scheetznicholas/cat6-cable-raceway/previews/cableraceway_plate_1.png

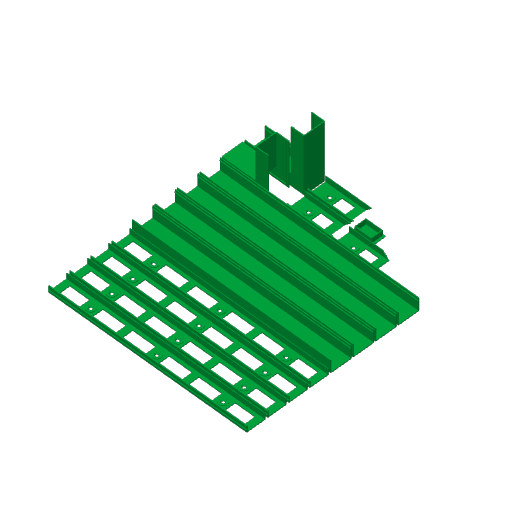
previews/cableraceway_plate_1.png
