scheetznicholas/cat6-cable-raceway/previews/cableraceway_plate_2.png

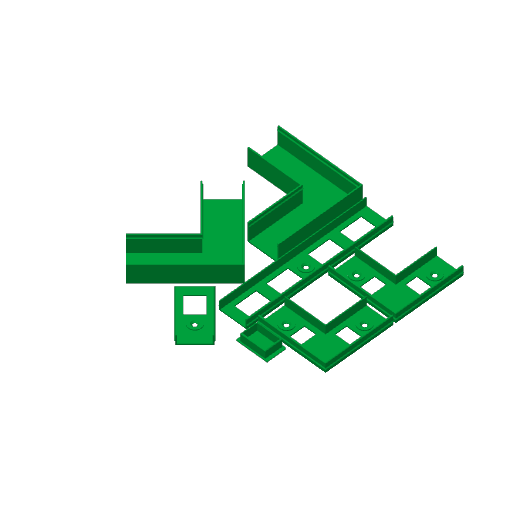
previews/cableraceway_plate_2.png
