scheetznicholas/cat6-cable-raceway/previews/corner_inside_base_stub_iso.png

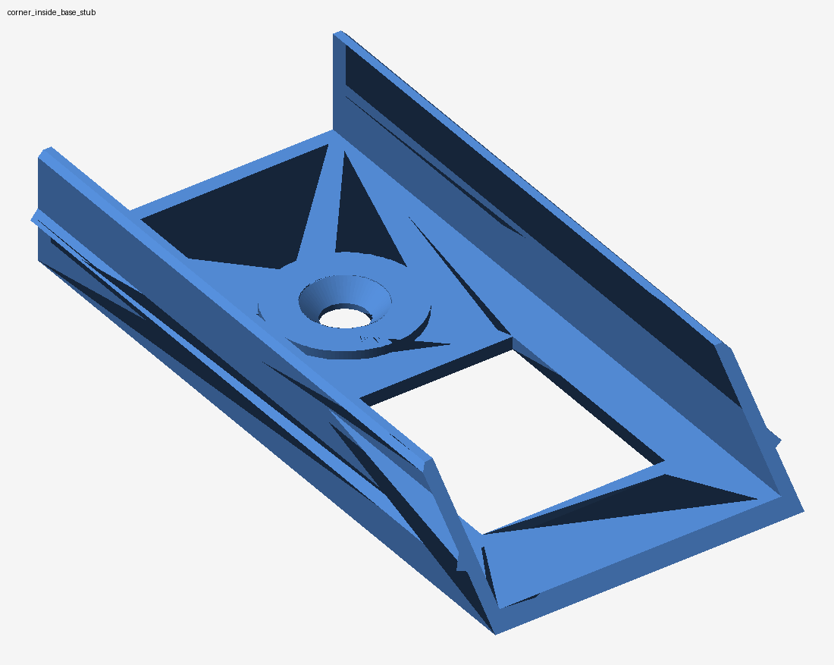
previews/corner_inside_base_stub_iso.png
