scheetznicholas/cat6-cable-raceway/previews/corner_inside_base_stub_under.png

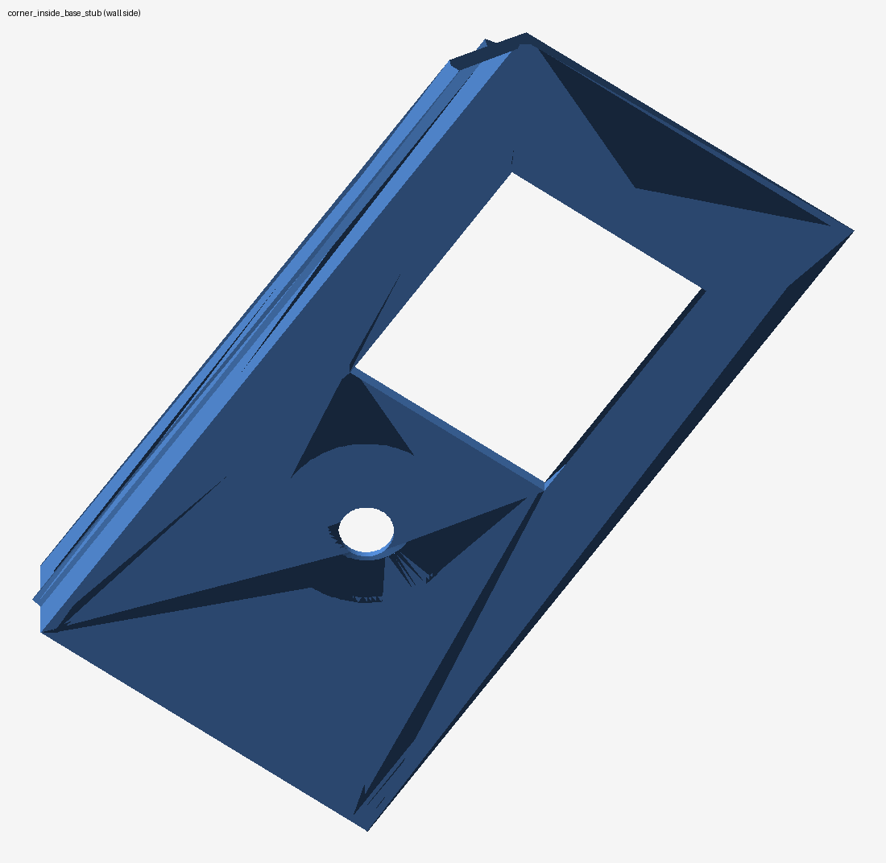
previews/corner_inside_base_stub_under.png
