scheetznicholas/cat6-cable-raceway/previews/corner_inside_cover_top.png

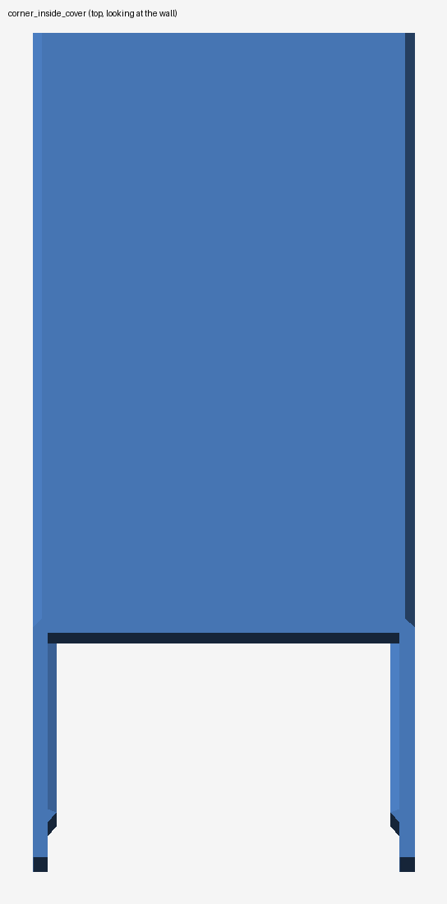
previews/corner_inside_cover_top.png
