scheetznicholas/cat6-cable-raceway/previews/corner_inside_cover_under.png

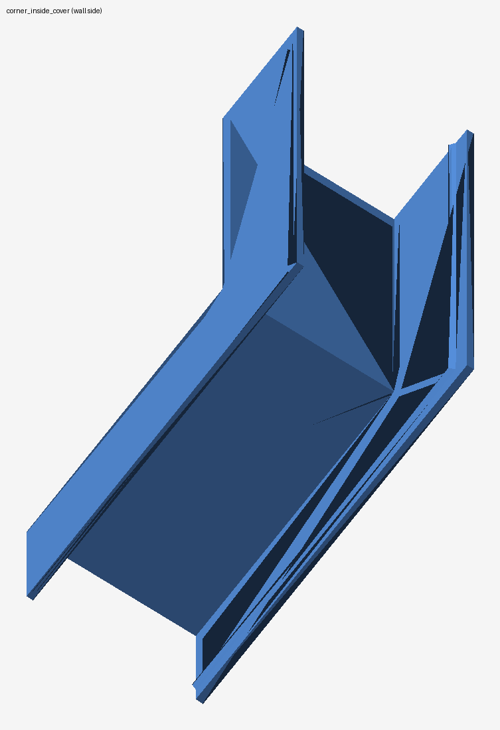
previews/corner_inside_cover_under.png
