scheetznicholas/cat6-cable-raceway/previews/corner_outside_base_stub_top.png

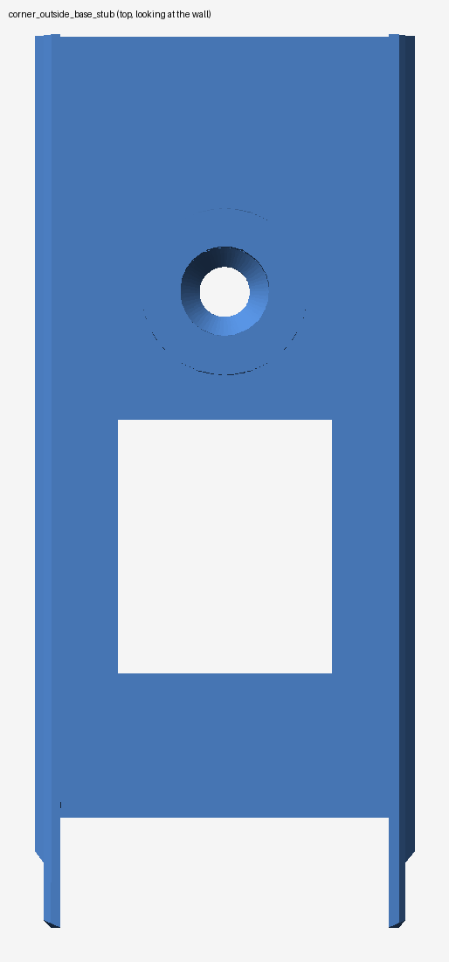
previews/corner_outside_base_stub_top.png
