scheetznicholas/cat6-cable-raceway/previews/corner_outside_cover_iso.png

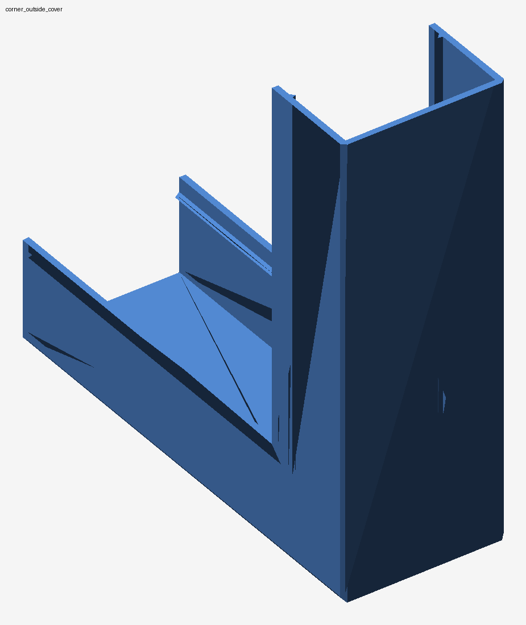
previews/corner_outside_cover_iso.png
