scheetznicholas/cat6-cable-raceway/previews/corner_outside_cover_top.png

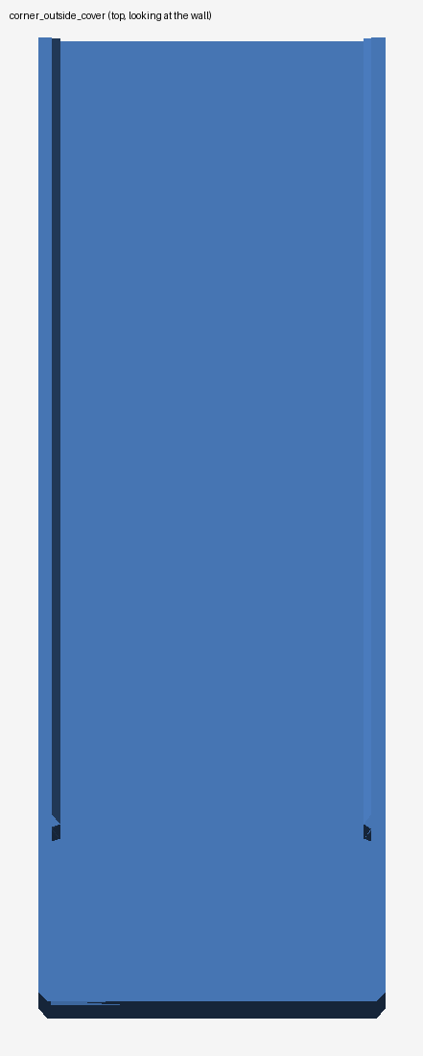
previews/corner_outside_cover_top.png
