scheetznicholas/cat6-cable-raceway/previews/corner_outside_cover_under.png

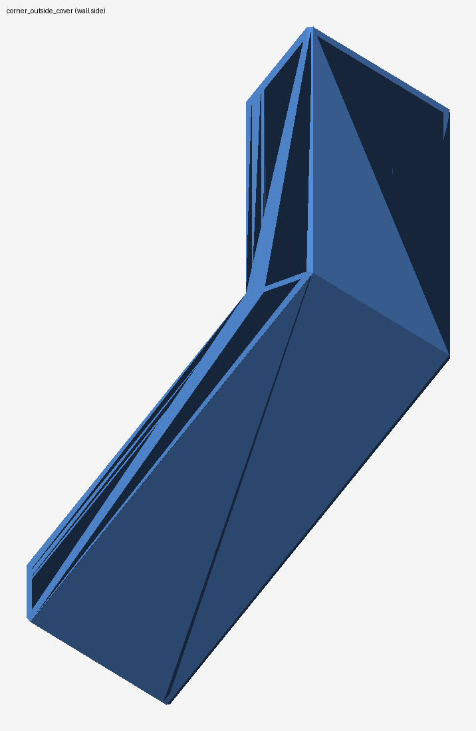
previews/corner_outside_cover_under.png
