scheetznicholas/cat6-cable-raceway/previews/elbow_flat_base_iso.png

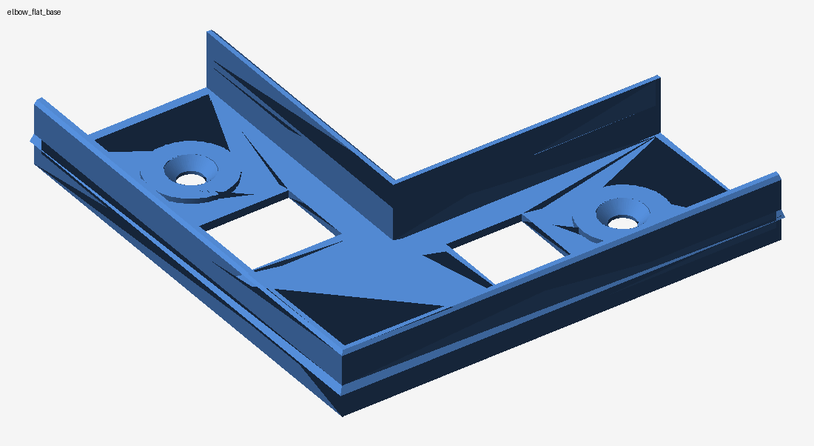
previews/elbow_flat_base_iso.png
