scheetznicholas/cat6-cable-raceway/previews/elbow_flat_base_under.png

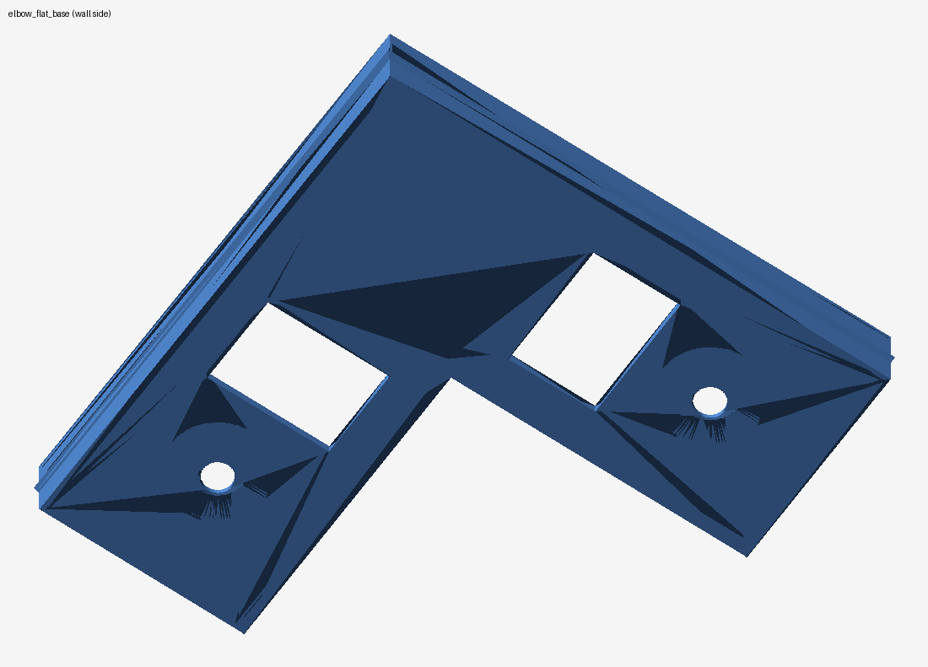
previews/elbow_flat_base_under.png
