scheetznicholas/cat6-cable-raceway/previews/elbow_flat_cover_iso.png

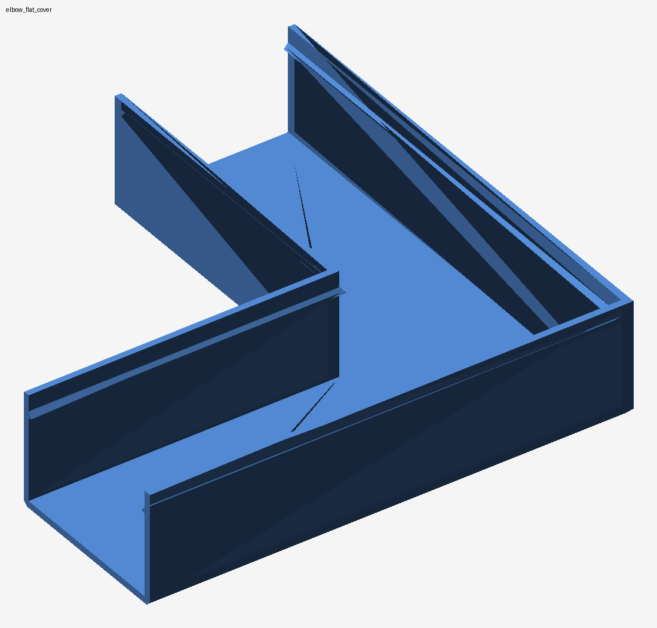
previews/elbow_flat_cover_iso.png
