scheetznicholas/cat6-cable-raceway/previews/elbow_flat_cover_top.png

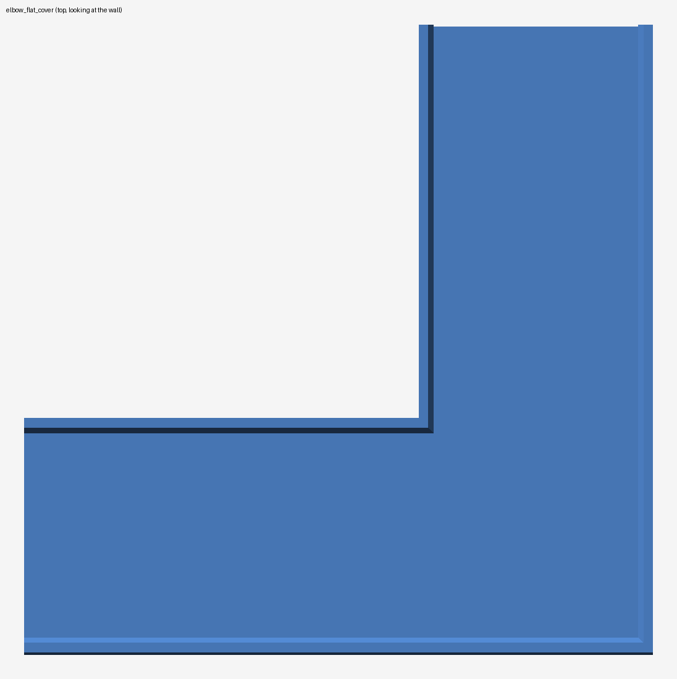
previews/elbow_flat_cover_top.png
