scheetznicholas/cat6-cable-raceway/previews/elbow_flat_cover_under.png

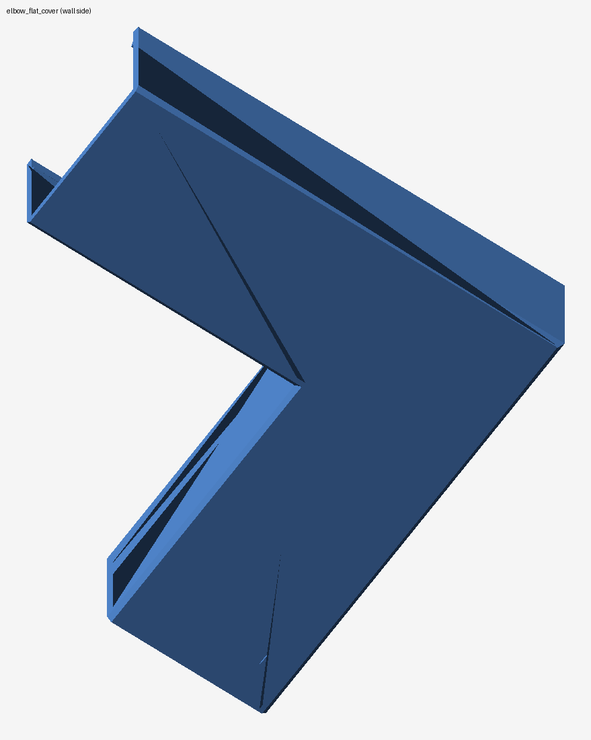
previews/elbow_flat_cover_under.png
