scheetznicholas/cat6-cable-raceway/previews/end_cap_iso.png

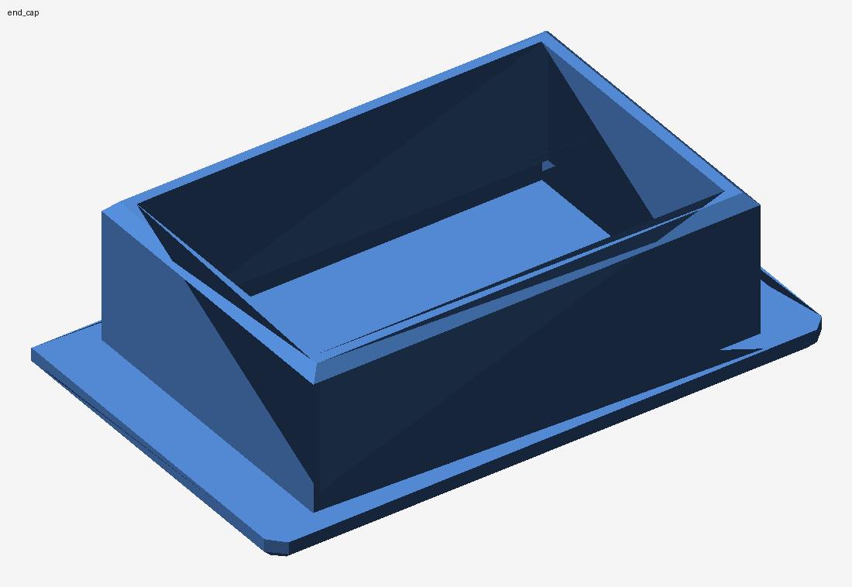
previews/end_cap_iso.png
