scheetznicholas/cat6-cable-raceway/previews/end_cap_top.png

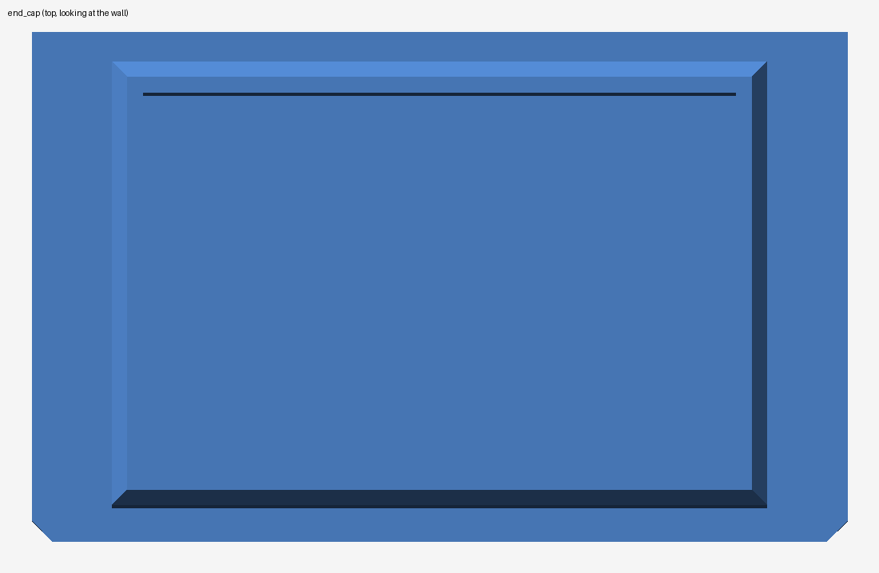
previews/end_cap_top.png
