scheetznicholas/cat6-cable-raceway/previews/end_cap_under.png

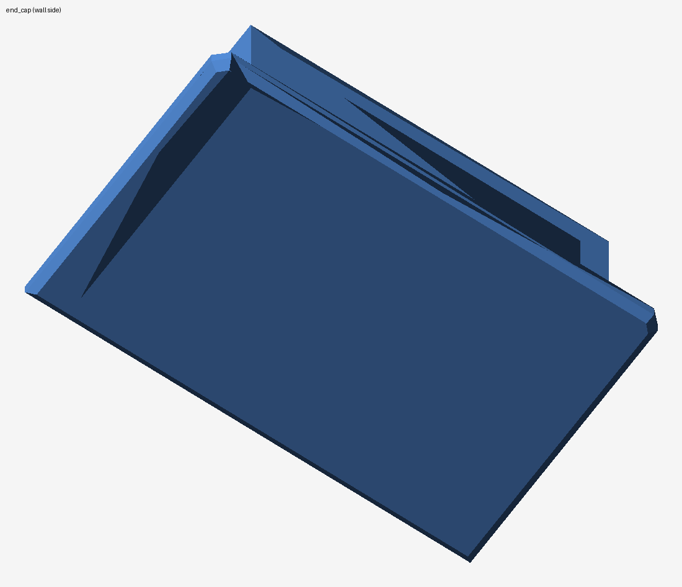
previews/end_cap_under.png
