scheetznicholas/cat6-cable-raceway/previews/straight_base_150_top.png

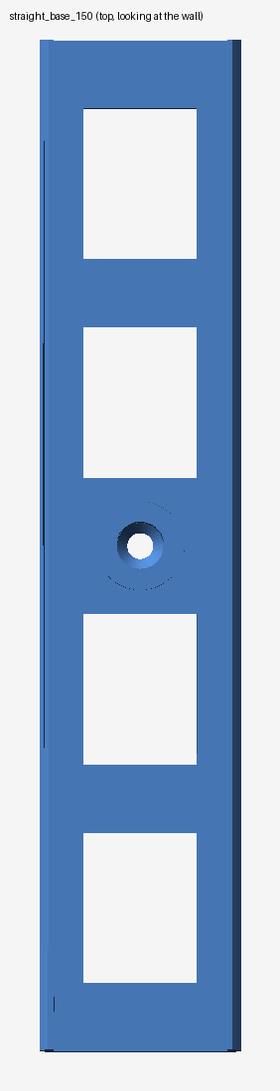
previews/straight_base_150_top.png
