scheetznicholas/cat6-cable-raceway/previews/straight_base_150_under.png

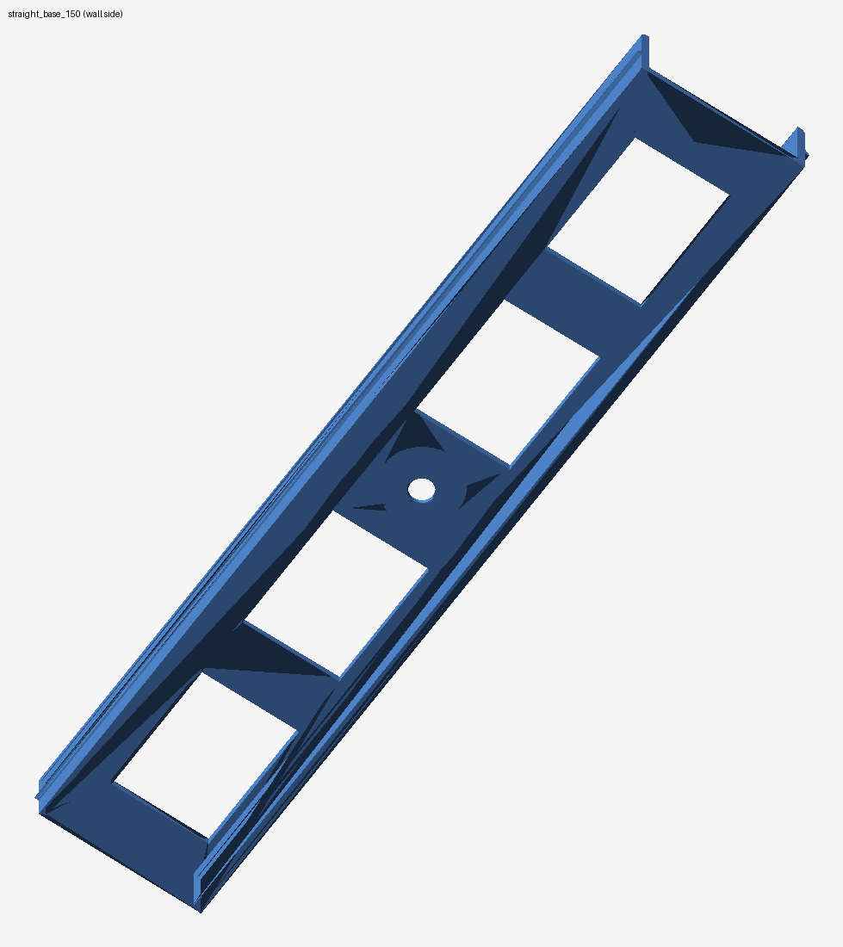
previews/straight_base_150_under.png
