scheetznicholas/cat6-cable-raceway/previews/straight_base_300_iso.png

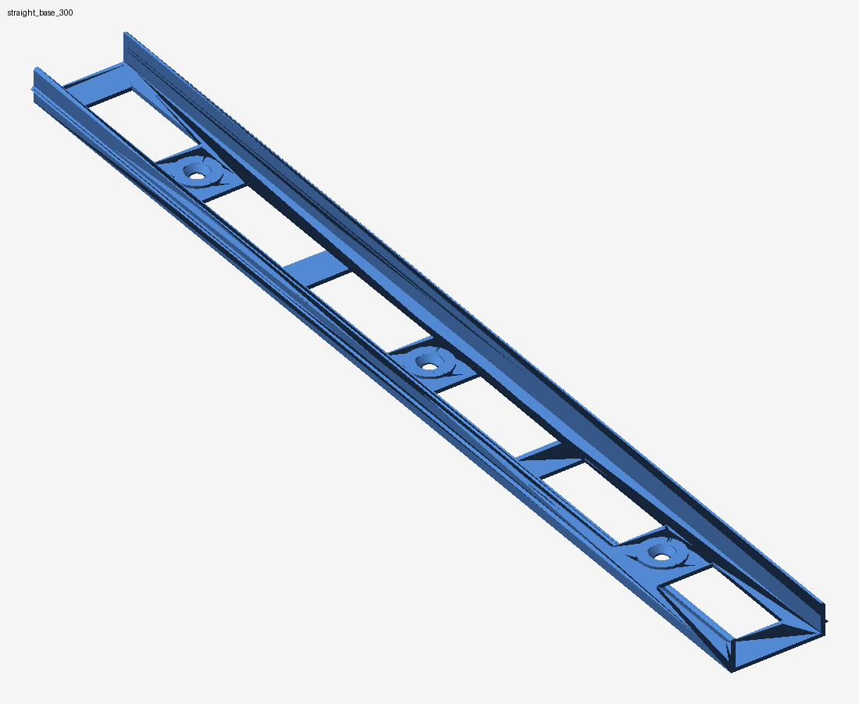
previews/straight_base_300_iso.png
