scheetznicholas/cat6-cable-raceway/previews/straight_base_300_under.png

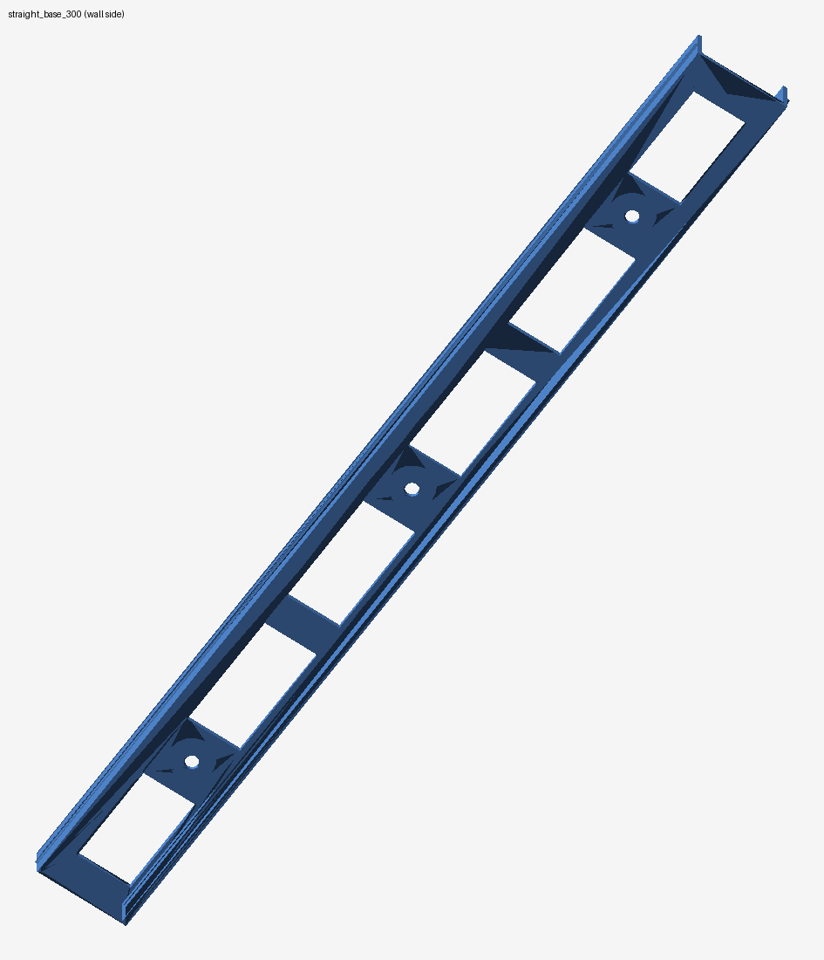
previews/straight_base_300_under.png
