scheetznicholas/cat6-cable-raceway/previews/straight_cover_300_iso.png

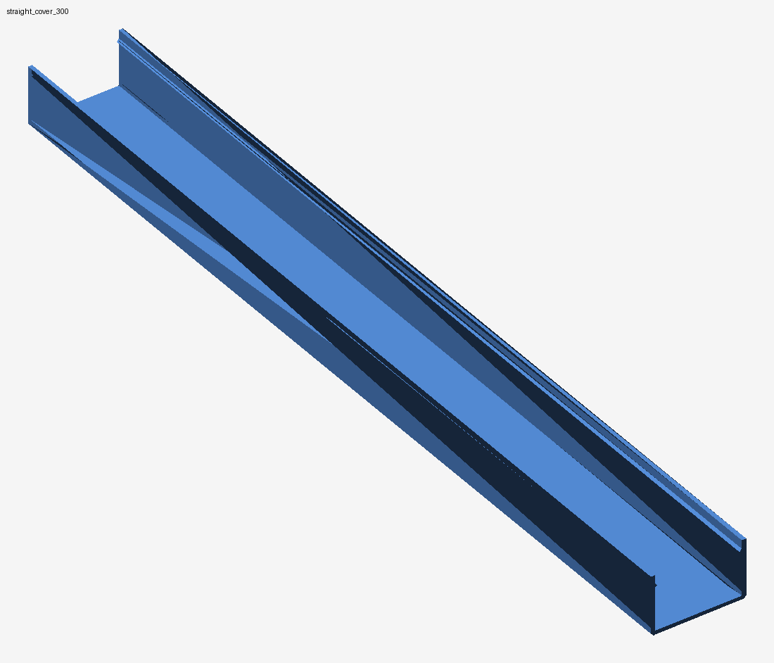
previews/straight_cover_300_iso.png
