scheetznicholas/cat6-cable-raceway/previews/straight_cover_300_under.png

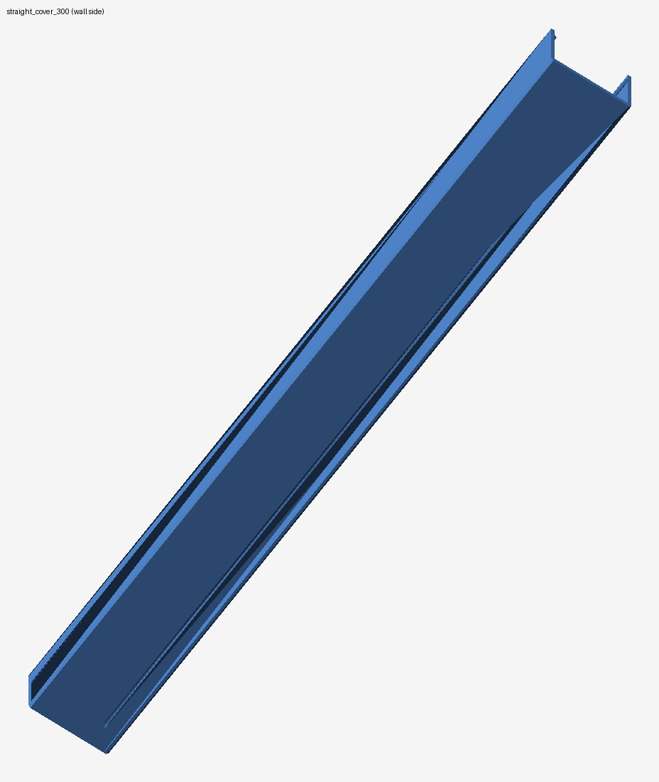
previews/straight_cover_300_under.png
