scheetznicholas/cat6-cable-raceway/previews/wallentry_plate_1.png

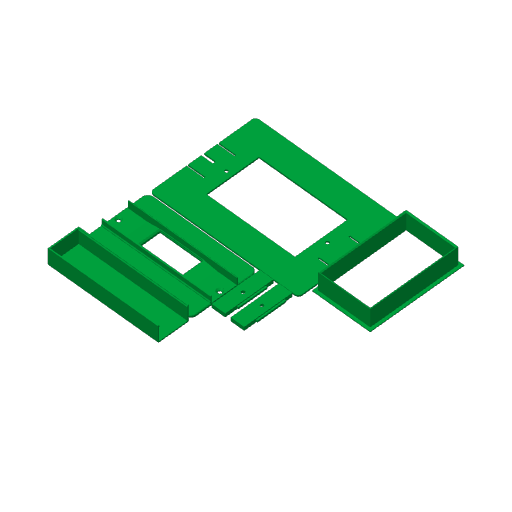
previews/wallentry_plate_1.png
