scheetznicholas/cat6-cable-raceway/previews/wallplate_face.png

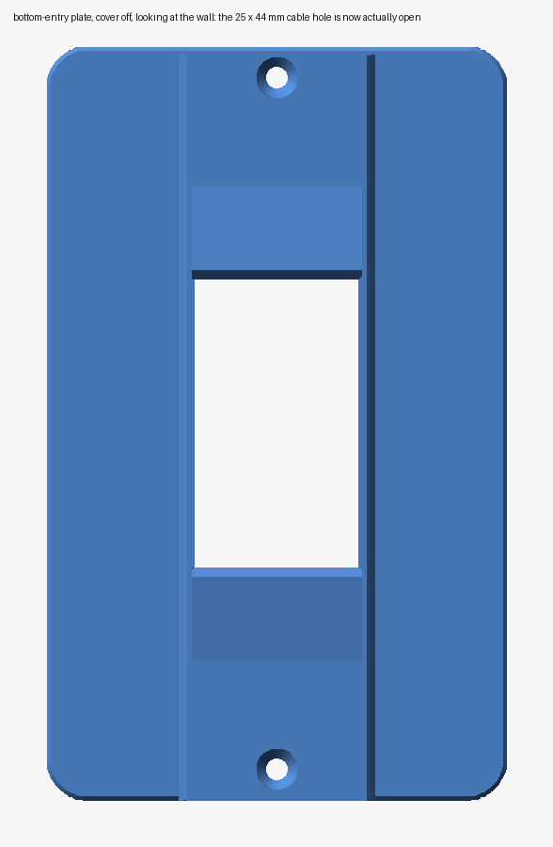
previews/wallplate_face.png
