scheetznicholas/cat6-cable-raceway/previews/wallplate_iso.png

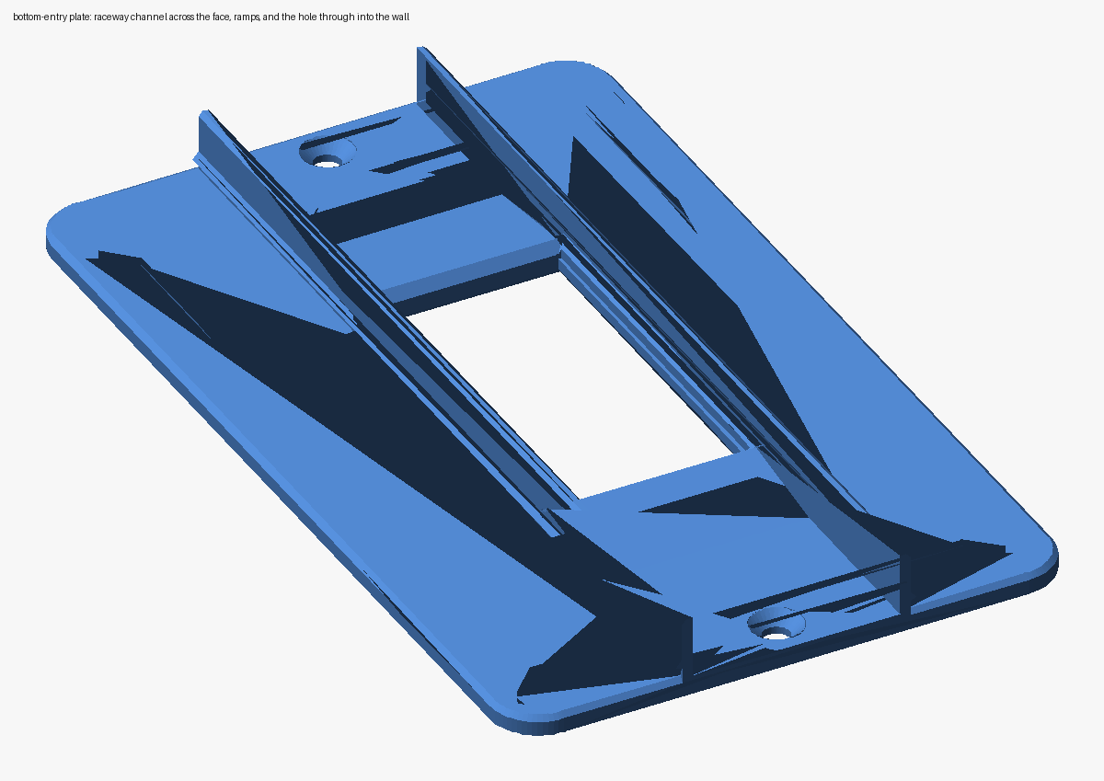
previews/wallplate_iso.png
