scheetznicholas/cat6-cable-raceway/stl/straight_cover_300.stl

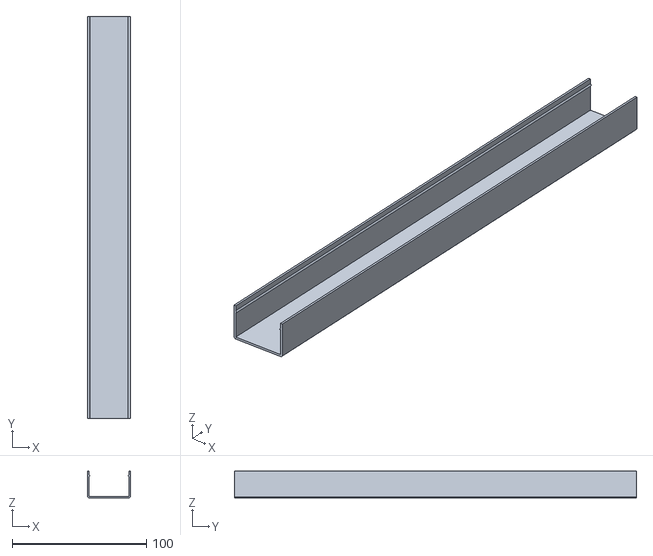
[picture p50: CAD file, 2026-09-24]
stl/straight_cover_300.stl
32.0 x 300.0 x 20.0
