scheetznicholas/cat6-cable-raceway/stl/elbow_flat_base.stl

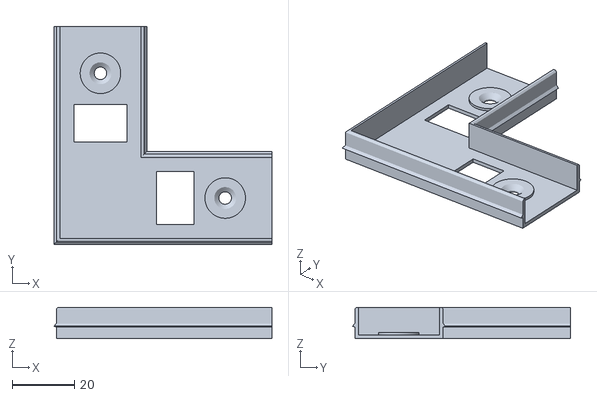
[picture p51: CAD file, 2026-09-24]
stl/elbow_flat_base.stl
69.9 x 69.9 x 10.0
