scheetznicholas/cat6-cable-raceway/stl/straight_base_300.stl

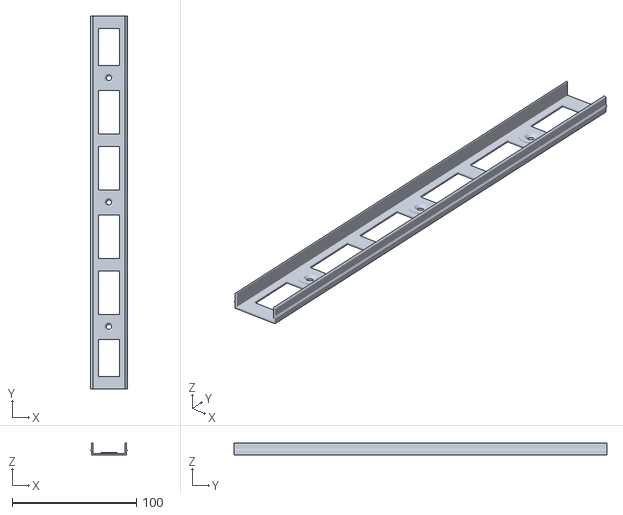
[picture p52: CAD file, 2026-09-24]
stl/straight_base_300.stl
29.8 x 300.0 x 10.0
