scheetznicholas/cat6-cable-raceway/stl/elbow_flat_cover.stl

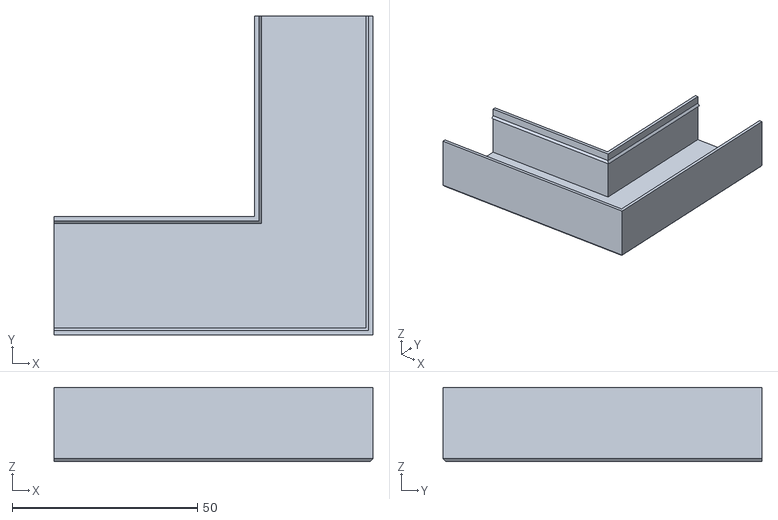
[picture p53: CAD file, 2026-09-24]
stl/elbow_flat_cover.stl
86.0 x 86.0 x 20.0
