scheetznicholas/cat6-cable-raceway/stl/corner_inside_cover.stl

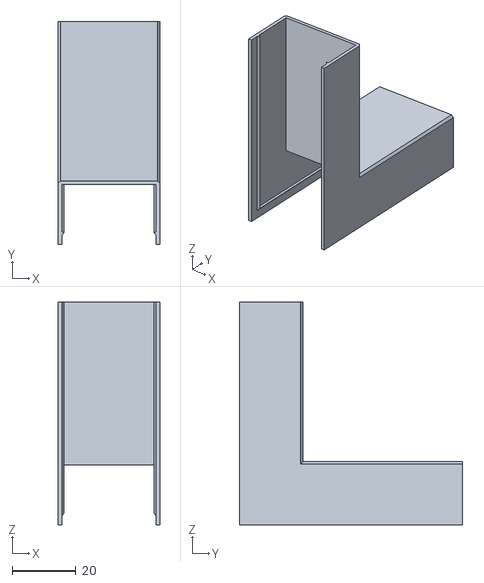
[picture p54: CAD file, 2026-09-24]
stl/corner_inside_cover.stl
32.0 x 70.0 x 70.0
